arnakke/thermostat/firmware/main/TemperatureSensor.cpp

/*
 * TemperatureSensor.cpp - Thermistor based temperature sensor class
 * implementation
 *
 * Copyright 2017 Marcel Clausen
 *
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
 */

#include "TemperatureSensor.hpp"
#include <math.h>


TemperatureSensor::TemperatureSensor(ADC&& thermistor_channel,
		ADC&& reference_channel) :
		thermistor(thermistor_channel),
		reference(reference_channel)
{
}


float TemperatureSensor::read()
{
	float ref_voltage = 2 * reference.read_voltage_avg(samples);
	float fraction = thermistor.read_voltage_avg(samples) / ref_voltage;
	float Rntc = fraction * R_upper / (1.0f - fraction);

	// Temperature from B-parameter equation
	float kelvin = 1.0f / (1.0f / 298.15f + log(Rntc / Rntc25) / Bntc);

	// Return celsius
	return kelvin - 273.15f;
}
